helan-y/HE-Synth/Journal Images/log_2.4.png

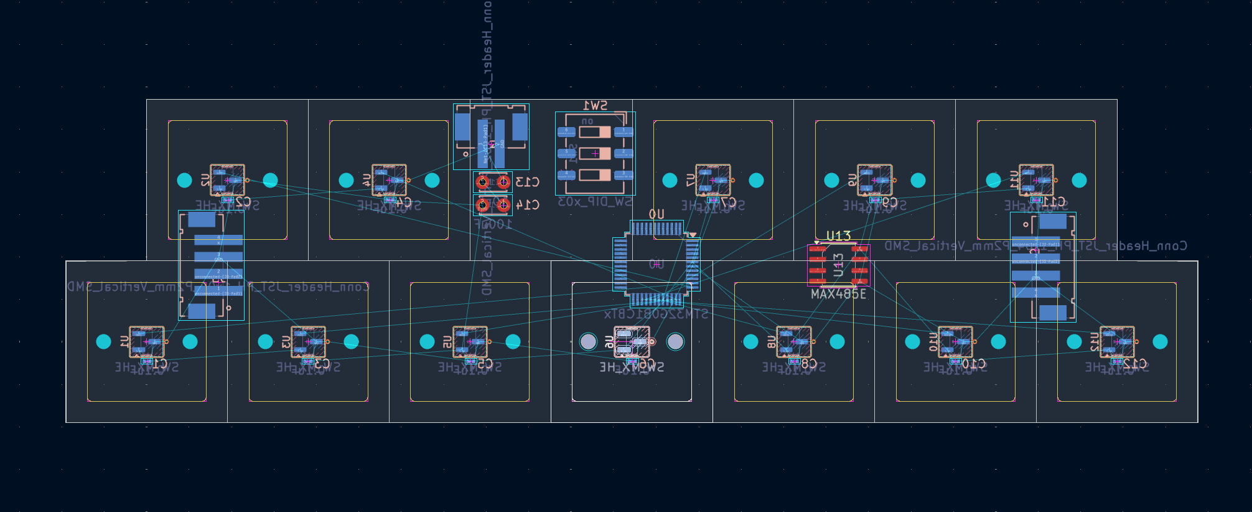
Journal Images/log_2.4.png
